anton-stolz/arm-rover/src/my_fast_bringup/config/ekf.yaml

ekf_filter_node:
  ros__parameters:
    frequency: 40.0
    sensor_timeout: 0.1
    two_d_mode: true
    publish_tf: true
    transform_time_offset: 0.0
    transform_timeout: 0.0
    print_diagnostics: false

    map_frame: map
    odom_frame: odom
    base_link_frame: base_link
    world_frame: odom

    # 1. The Wheel Encoders (only use X velocity)
    odom0: wheel/odom
    odom0_config: [false, false, false,
                   false, false, false,
                   true,  false, false,
                   false, false, false,
                   false, false, false]
    odom0_queue_size: 10
    odom0_differential: false
    odom0_relative: false

    # 2. The IMU (only use Yaw velocity / Angular Z)
    imu0: imu/data_raw
    imu0_config: [false, false, false,
                  false, false, false,
                  false, false, false,
                  false, false, true,
                  false, false, false]
    imu0_queue_size: 10
    imu0_differential: false
    imu0_relative: false
    imu0_remove_gravitational_acceleration: true
